mjohannessen/halloween_skulls/halloween-skull/renders/back.png

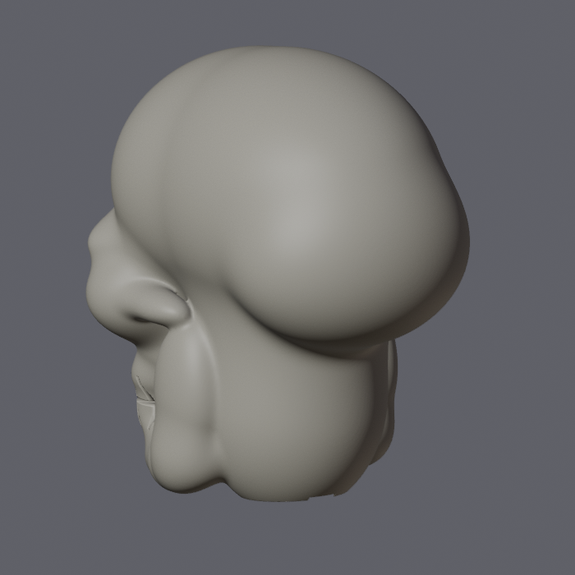
halloween-skull/renders/back.png
