mjohannessen/halloween_skulls/halloween-skull/renders/base_bottom.png

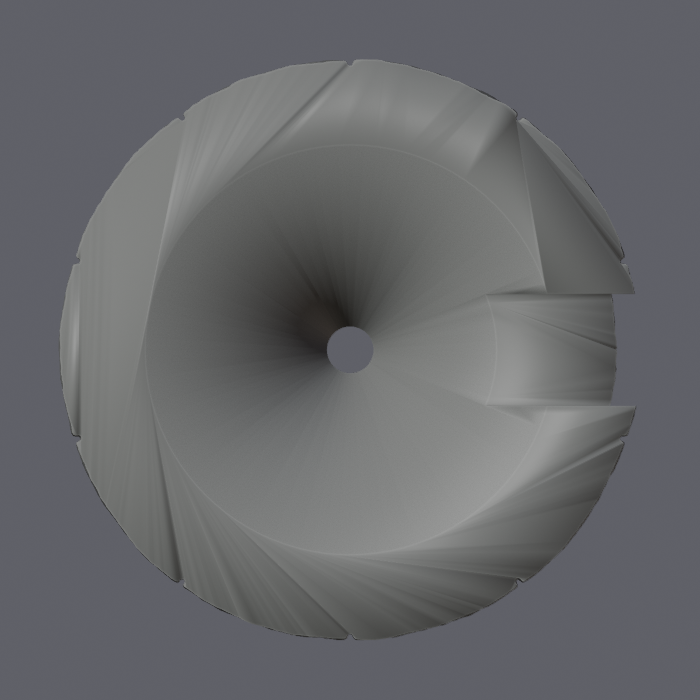
halloween-skull/renders/base_bottom.png
