mjohannessen/halloween_skulls/halloween-skull/renders/base_section.png

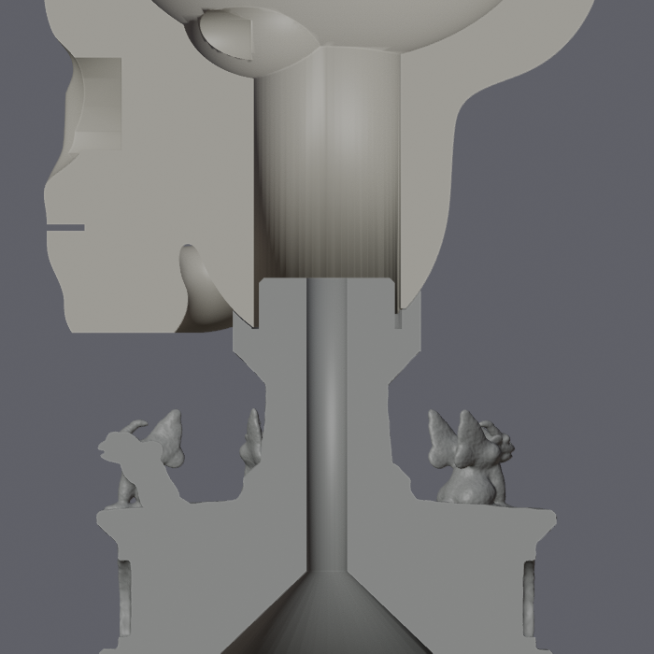
halloween-skull/renders/base_section.png
