mjohannessen/halloween_skulls/halloween-skull/renders/base_three_quarter.png

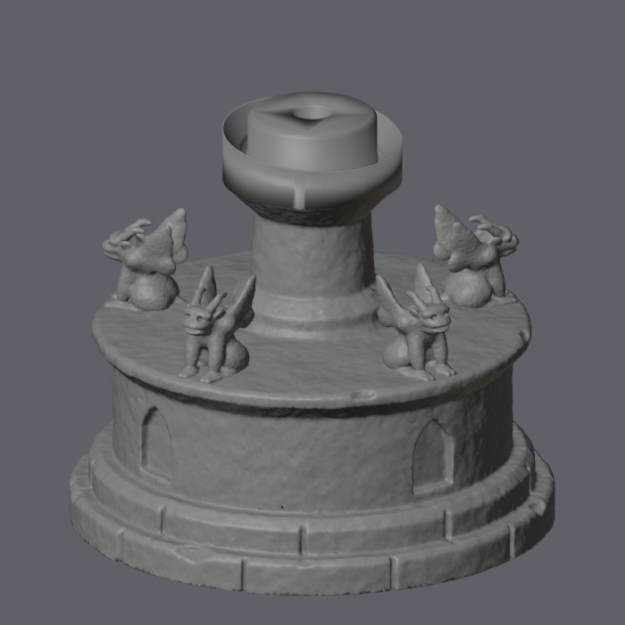
halloween-skull/renders/base_three_quarter.png
