mjohannessen/halloween_skulls/halloween-skull/renders/section_center.png

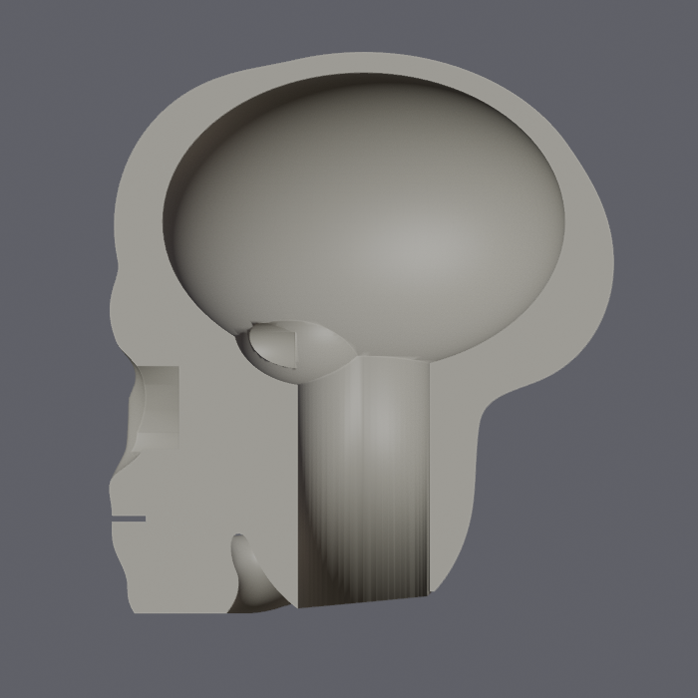
halloween-skull/renders/section_center.png
