mjohannessen/halloween_skulls/halloween-skull/renders/side.png

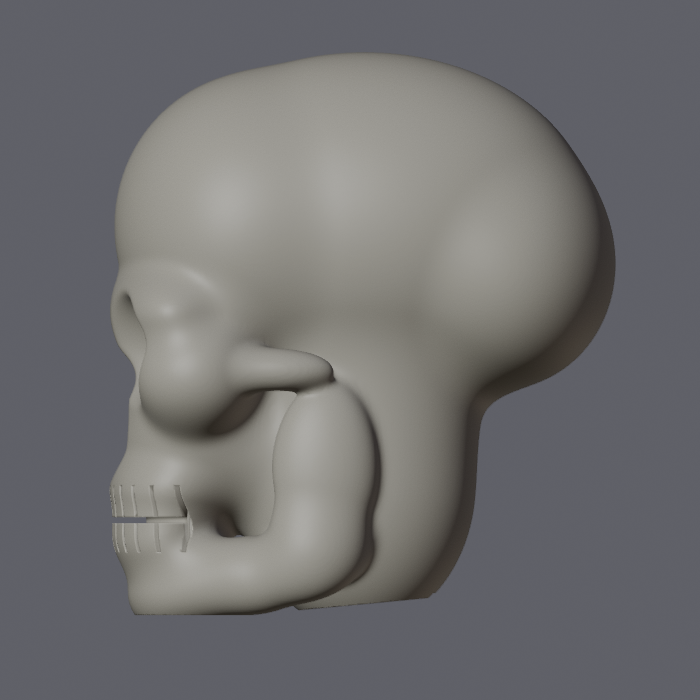
halloween-skull/renders/side.png
