mjohannessen/halloween_skulls/halloween-skull/renders/three_quarter.png

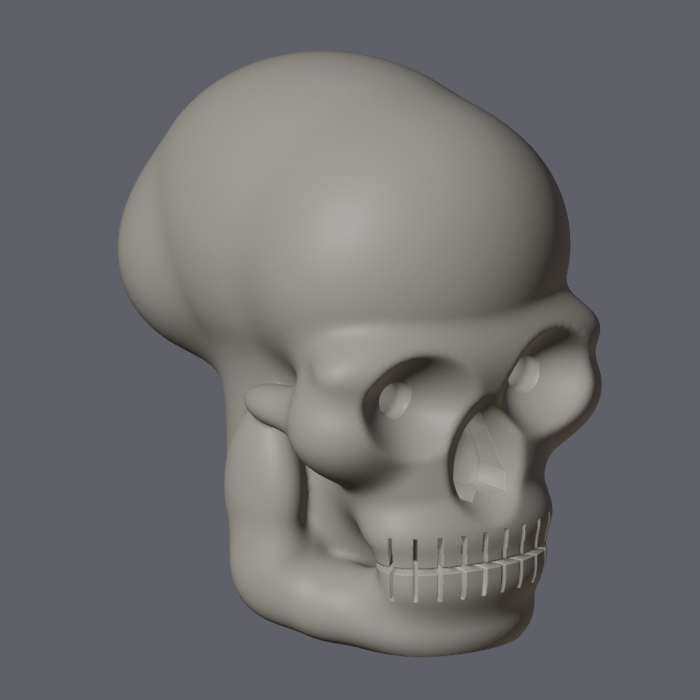
halloween-skull/renders/three_quarter.png
