mjohannessen/halloween_skulls/halloween-skull/renders/assembly_front.png

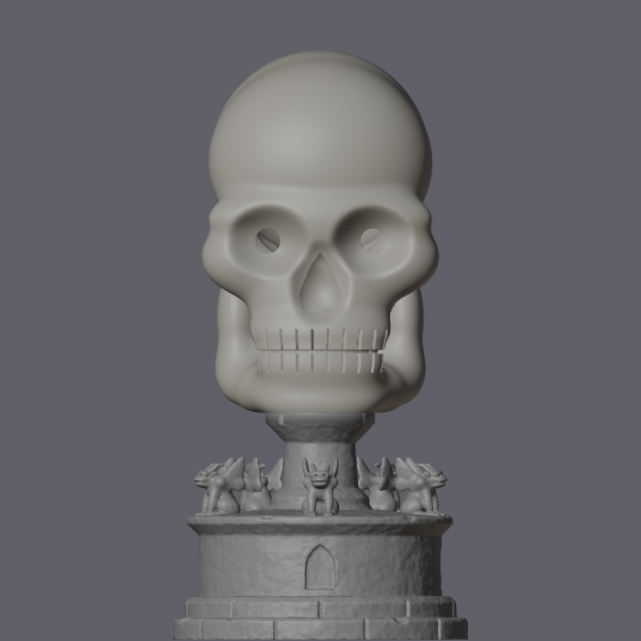
halloween-skull/renders/assembly_front.png
