mjohannessen/halloween_skulls/halloween-skull/renders/assembly_side.png

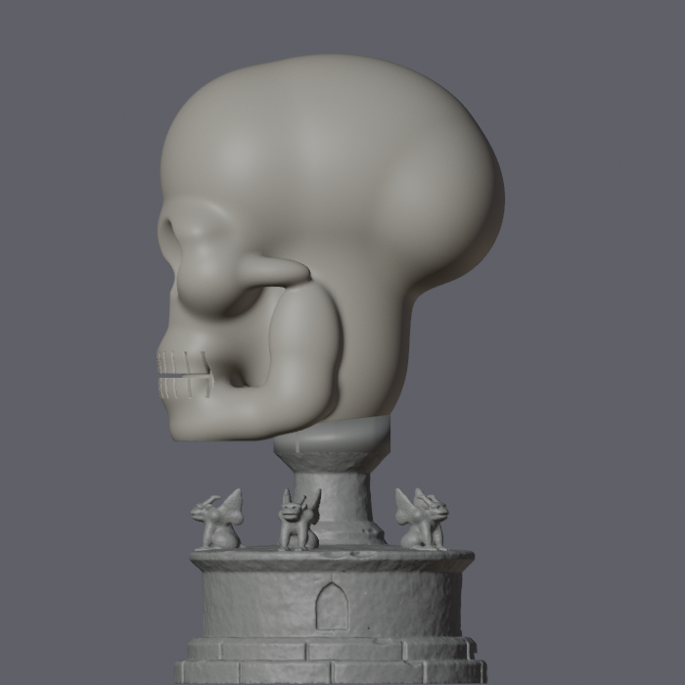
halloween-skull/renders/assembly_side.png
