mjohannessen/halloween_skulls/halloween-skull/renders/assembly_three_quarter.png

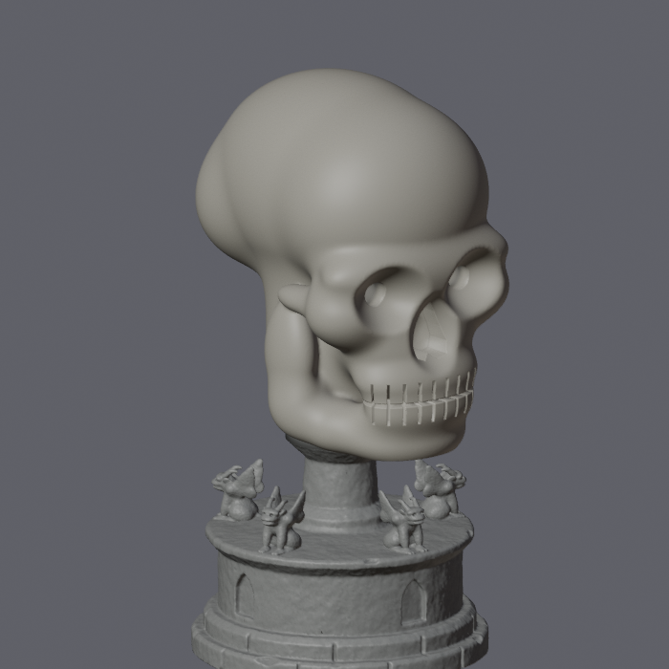
halloween-skull/renders/assembly_three_quarter.png
